skemake/LJUSSABEL/Hardware/Board/20216-09-29.png

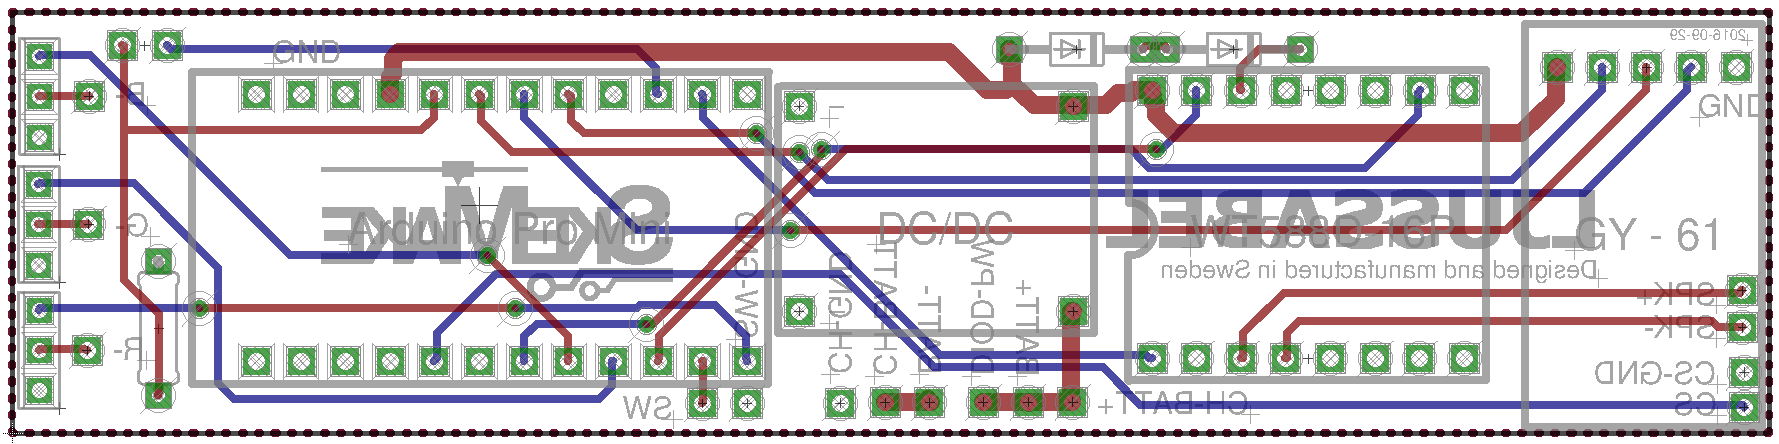
Hardware/Board/20216-09-29.png
